NJurquet/FBG/BIG_BOT/src/hardware/servoMotor.py

from gpiozero import Servo

class ServoMotor:
    """
        Class to control a servo motor

        Parameters:
            name (str): The name of the servo motor.
            pin (int): The pin number the servo motor is connected to.

        Methods:
            setAngle(angle): Sets the angle of the servo motor.
            stop(): Stops the servo motor.
    """
    def __init__(self, name: str, pin: int):
        pwmCorrection = 0.45
        maxPWM = (2.0+pwmCorrection)/1000
        minPWM = (1.0-pwmCorrection)/1000

        self.name = name
        self.servo = Servo(pin, min_pulse_width=minPWM, max_pulse_width=maxPWM)
        self.angle = 0

    def setAngle(self, angle: int):
        """
        Sets the goal angle of the servo motor.

        Parameters:
            angle (float): The goal angle (between -1 and 1).
        """
        self.angle = angle
        self.servo.value = self.angle

    def stop(self):
        """
            Stops the servo motor.
        """
        self.servo.detach()
