NJurquet/FBG/BIG_BOT/src/fsm/commands/initCommands.py

from .command import ICommand
from typing import TYPE_CHECKING
import time

if TYPE_CHECKING:
    from ..FSM import RobotFSM


class InitLCDCommand(ICommand):
    """
    Command to re-initialize the LCD screen of the robot after a power shutdown.
    
    Parameters:
        fsm (RobotFSM): The FSM instance of the robot.
    """
    def __init__(self, fsm: 'RobotFSM',):
        self._is_finished = False
        self.fsm = fsm

    def execute(self):
        self.fsm.robot.logger.info("InitLCDCommand : Initializing LCD...")
        self.fsm.robot.lcd.clear()
        self.fsm.robot.lcd.write_score(self.fsm.robot.score)

        self.finished()
    
    def stop(self):
        pass

    def pause(self):
        pass

    def resume(self):
        pass
    
    def finished(self):
        self.stop()
        self._is_finished = True
